codetiger/GameTiger/content/image_util/allGameAlphaSprite.png

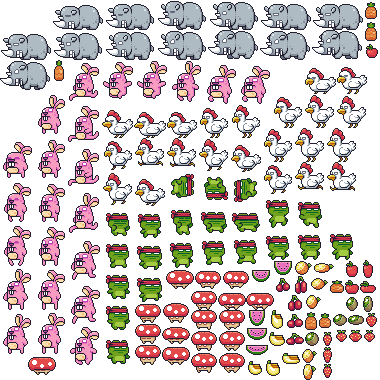
content/image_util/allGameAlphaSprite.png
