codetiger/GameTiger/content/image_util/allGameSprite.png

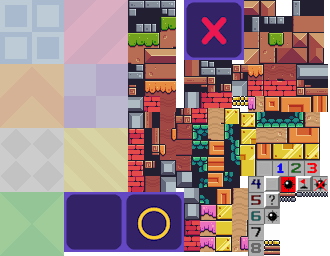
content/image_util/allGameSprite.png
