codetiger/GameTiger/content/image_util/menuSprite.png

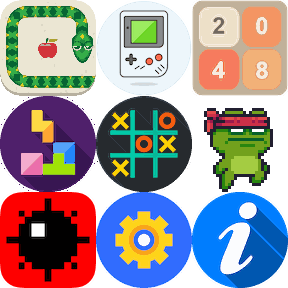
content/image_util/menuSprite.png
