codetiger/GameTiger/content/image_util/ninjafrog/terrain/terrain.png

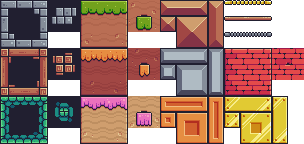
content/image_util/ninjafrog/terrain/terrain.png
