codetiger/GameTiger/content/image_util/original/about.png

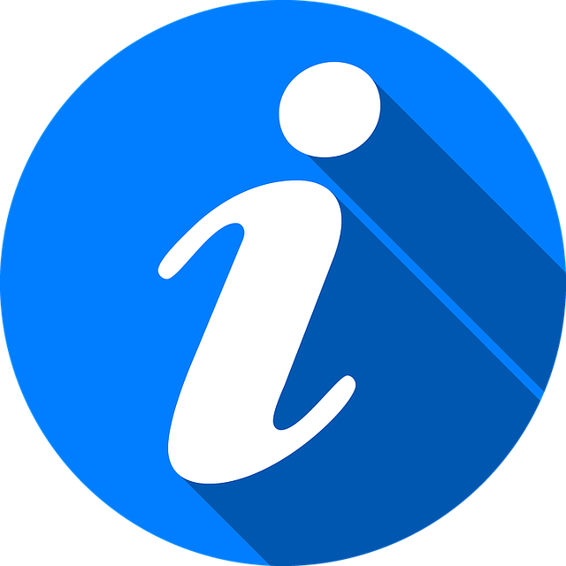
content/image_util/original/about.png
