codetiger/GameTiger/content/image_util/original/g2048.png

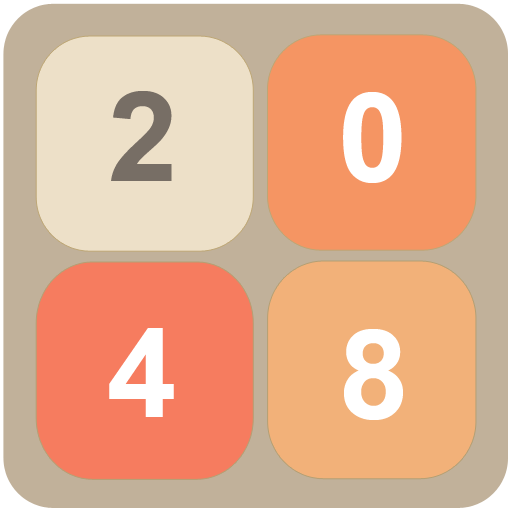
content/image_util/original/g2048.png
