codetiger/GameTiger/content/image_util/original/gameboy.png

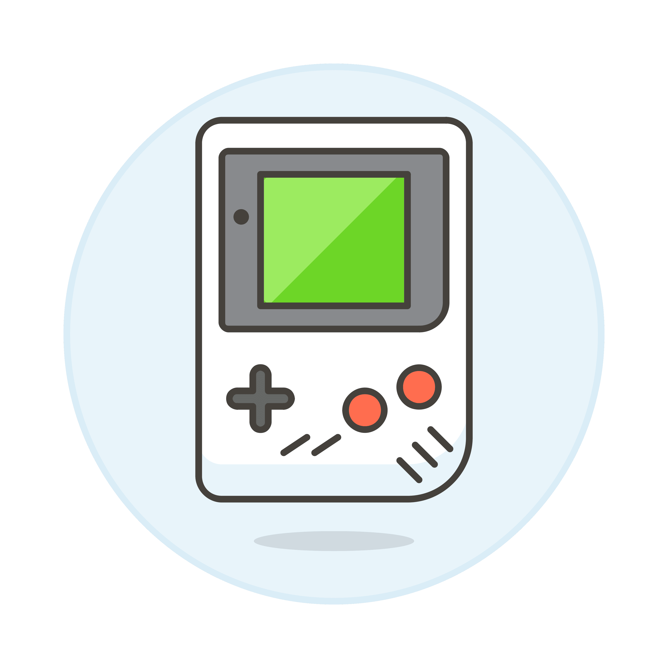
content/image_util/original/gameboy.png
