codetiger/GameTiger/content/image_util/original/mine.png

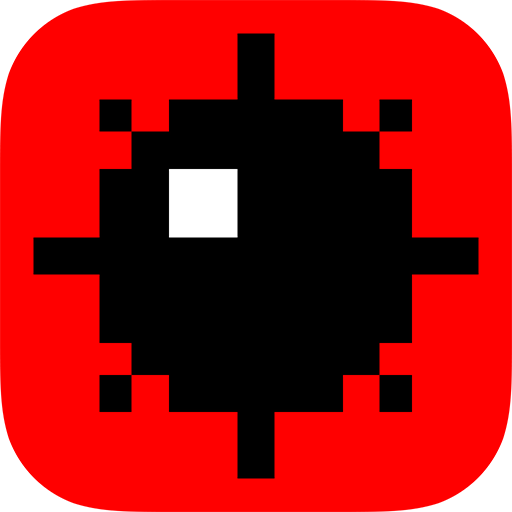
content/image_util/original/mine.png
