codetiger/GameTiger/content/image_util/original/settings.png

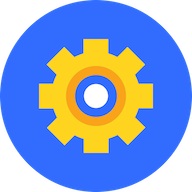
content/image_util/original/settings.png
