codetiger/GameTiger/content/image_util/original/snake.png

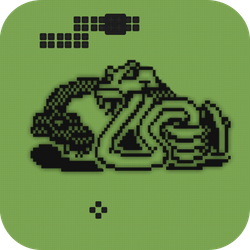
content/image_util/original/snake.png
