codetiger/GameTiger/content/image_util/original/ttt.png

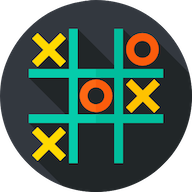
content/image_util/original/ttt.png
