codetiger/GameTiger/PCB/pcb-back.png

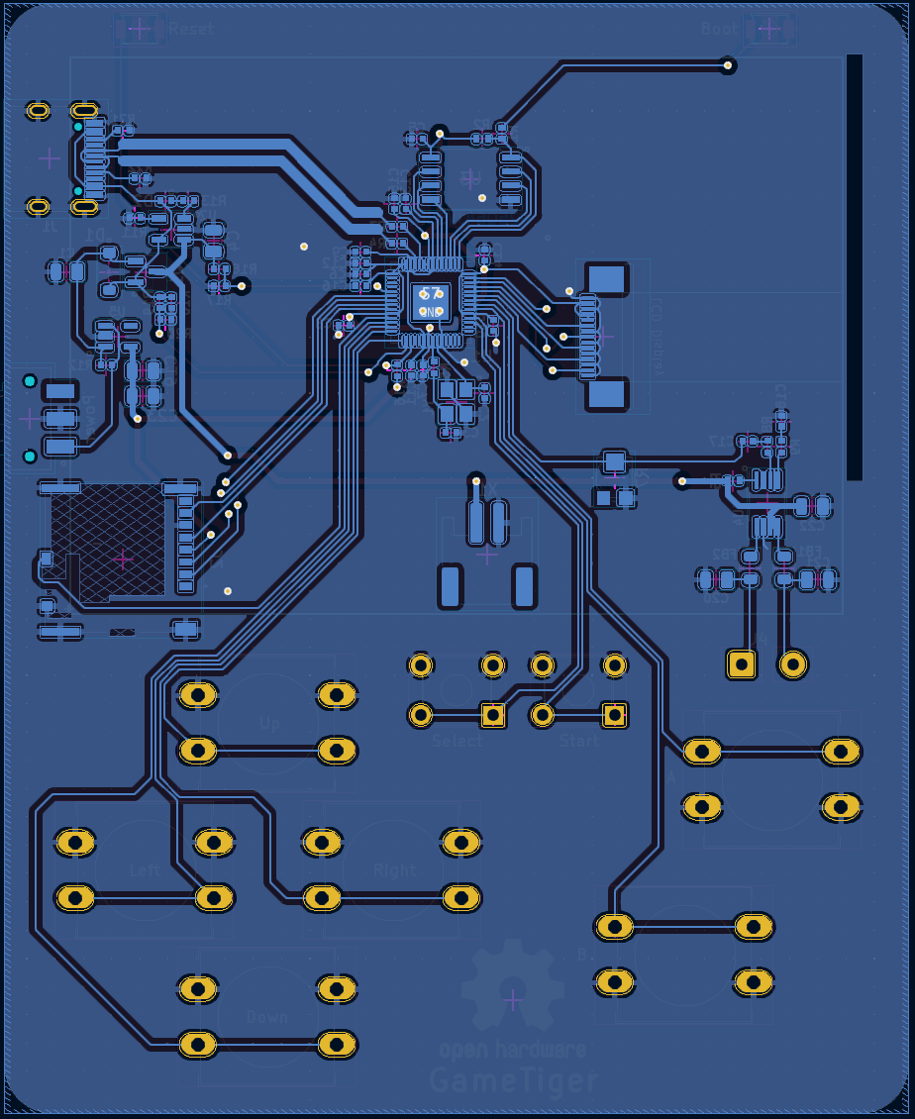
PCB/pcb-back.png
