codetiger/GameTiger/PCB/pcb-front.png

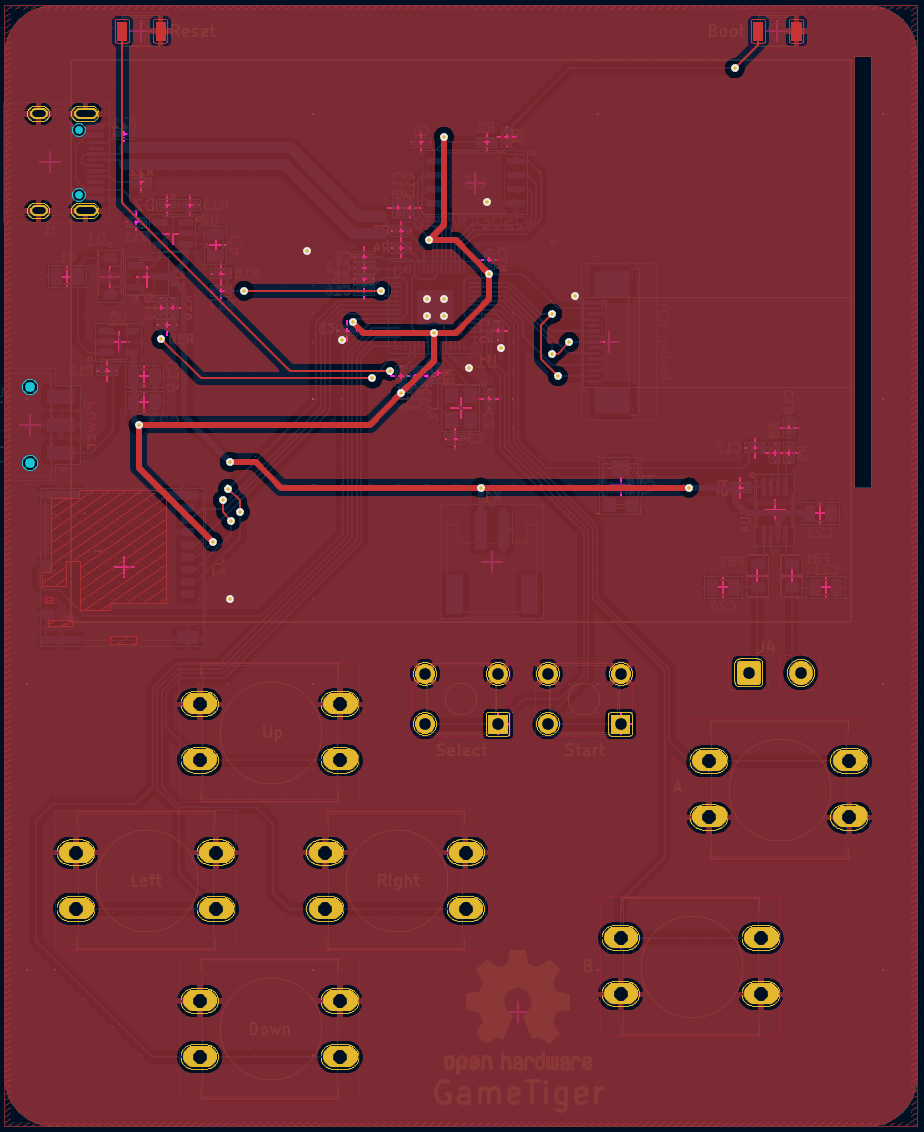
PCB/pcb-front.png
