codetiger/GameTiger/core/color.h

#include "common.h"

#ifndef _GAME_TIGER_COLOR_H
#define _GAME_TIGER_COLOR_H

#define div_255_fast(x) (((x) + (((x) + 257) >> 8)) >> 8)

typedef struct Color {
    union {
        uint16_t value;
        struct {
            uint16_t red:5;
            uint16_t green:6;
            uint16_t blue:5;
        } Colors;
    };

    Color() {
        Colors.red = 0; Colors.green = 0; Colors.blue = 0;
    }

    Color(uint8_t r, uint8_t g, uint8_t b) {
        Colors.red = r >> 3; Colors.green = g >> 2; Colors.blue = b >> 3;
    }

    Color(uint16_t v) {
        value = v;
    }

    Color(uint32_t v) {
        uint8_t r = (v & 0xFF0000) >> 16;
        uint8_t g = (v & 0x00FF00) >> 8;
        uint8_t b = (v & 0x0000FF) >> 0;
        Colors.red = r >> 3; 
        Colors.green = g >> 2; 
        Colors.blue = b >> 3;
    }

    Color& operator=(const uint16_t &v) {
        value = v;
        return *this;
    }

    void mix(const Color &c, uint8_t alpha) {
        uint8_t delta = 255 - alpha;
        Colors.red = div_255_fast(c.Colors.red * alpha + Colors.red * delta);
        Colors.green = div_255_fast(c.Colors.green * alpha + Colors.green * delta);
        Colors.blue = div_255_fast(c.Colors.blue * alpha + Colors.blue * delta);
    }

} Color;

#endif
